keegandewitt/Arp/hardware/enclosure/SCHEMDRAW_SUCCESS_RULES.md

# Schemdraw Success Rules - What Actually Works

**Date**: 2025-11-03
**Status**: VERIFIED - These rules produce clean, professional schematics

---

## THE GOLDEN RULES THAT WORK

### 1. **NO LABELS BEFORE CIRCUITS**
❌ **WRONG:**
```python
d += elm.Label().label('Section Title', fontsize=14)
d += elm.Gap().label(['+', 'INPUT', '−'])
```
Result: Title overlaps with the Gap element

✅ **CORRECT:**
```python
# Just draw the circuit, no titles
d += elm.Gap().label(['+', 'INPUT', '−'])
```

### 2. **USE d.push() AND d.pop() FOR BRANCHING**
✅ **CORRECT:**
```python
d += elm.Resistor().right().label('R1\n10kΩ')
d += elm.Dot()
d.push()  # Save position
d += elm.Resistor().down().label('R2\n10kΩ', loc='bot')
d += elm.Ground()
d.pop()  # Return to saved position
d += elm.Line().right()  # Continue from dot
```

### 3. **CONNECT TO SHARED RAILS WITH .toy() AND .tox()**
✅ **CORRECT:**
```python
# Create power rail at top
d += elm.Line().right().length(d.unit*6)
d.push()
d += elm.Vdd().label('3.3V')
d.pop()
rail_top = d.here[1]

# Later, connect diode to rail
d += elm.Diode().up().label('D1\nBAT85')
d += elm.Line().toy(rail_top)  # Connect to saved Y coordinate
```

### 4. **SAVE POSITIONS FOR LATER REFERENCE**
✅ **CORRECT:**
```python
d += elm.Resistor().right().label('R1\n10kΩ')
d += elm.Dot()
tap_position = d.here  # Save this coordinate
d.push()
d += elm.Resistor().down().label('R2\n10kΩ', loc='bot')
bottom_position = d.here  # Save this too
d.pop()

# Later, use saved positions
d += elm.Line().at(bottom_position).down().toy(ground_rail)
```

### 5. **USE .at() TO POSITION INDEPENDENT CIRCUITS**
✅ **CORRECT:**
```python
# First circuit
d.here = (0, 10)
d += elm.Gap().label(['+', 'INPUT 1', '−'])
# ... circuit 1

# Second circuit below it
d.here = (0, 5)  # Manually position
d += elm.Gap().label(['+', 'INPUT 2', '−'])
# ... circuit 2
```

### 6. **STANDARD SPACING VALUES**
✅ **WORKING VALUES:**
```python
d.config(fontsize=11, unit=2.5)

# Vertical spacing between circuits
d.here = (0, d.here[1] - d.unit*3)  # 3 units between circuits

# Horizontal spacing for rails
d += elm.Line().right().length(d.unit*6)  # 6 units for rail length
```

### 7. **AVOID SPECIAL CHARACTERS IN LABELS**
❌ **BREAKS:**
```python
.label('100Ω')  # Omega symbol breaks XML parsing
.label('M4 D4 → DAC')  # Arrow breaks XML parsing
.label('DAC & LED')  # Ampersand breaks XML parsing
```

✅ **WORKS:**
```python
.label('100ohm')
.label('M4 D4 to DAC')
.label('DAC and LED')
```

### 8. **COMPLETE CIRCUIT TEMPLATE**
✅ **PROVEN WORKING PATTERN:**
```python
import schemdraw
from schemdraw import elements as elm

with schemdraw.Drawing() as d:
    d.config(fontsize=11, unit=2.5)

    # Power rail at top
    d += elm.Line().right().length(d.unit*6)
    d.push()
    d += elm.Vdd().label('3.3V')
    d.pop()
    rail_top = d.here[1]

    # Circuit 1
    d.here = (0, d.here[1] - d.unit*1.5)
    d += elm.Gap().label(['+', 'INPUT', '−'])
    d.push()
    d += elm.Resistor().right().label('R1\n10kΩ')
    d += elm.Dot()
    d.push()
    d += elm.Resistor().down().label('R2\n10kΩ', loc='bot')
    r2_bottom = d.here
    d.pop()
    d += elm.Line().right()
    d.push()
    d += elm.Diode().up().label('D1\nBAT85')
    d += elm.Line().toy(rail_top)
    d.pop()
    d += elm.Line().right()
    d += elm.Dot(open=True).label('OUTPUT', loc='right')

    # Ground rail at bottom
    d.here = (0, r2_bottom[1] - d.unit*0.5)
    d += elm.Line().right().length(d.unit*6)
    d += elm.Ground()

    # Connect circuit to ground rail
    d += elm.Line().at(r2_bottom).down().toy(d.here[1])

d.save('schematic.svg')
```

---

## WHAT DOESN'T WORK

### ❌ Adding section labels before circuits
Creates overlapping text on components

### ❌ Using `.at(x, y)` with calculated coordinates for everything
Over-complicated, hard to maintain

### ❌ Mixing Label elements with circuits
Labels should only be on components, not floating

### ❌ Forgetting to save positions
Can't connect things later without saved coordinates

### ❌ Unicode symbols in labels
Breaks XML parsing (Ω, →, &, etc.)

---

## KEY INSIGHTS

1. **Schemdraw uses sequential chaining** - each element continues from the previous
2. **Use d.push()/d.pop() to branch** - not complex coordinate math
3. **Save positions with variables** - `pos = d.here` for later reference
4. **Use .toy() and .tox()** - to align with saved positions
5. **Keep it simple** - the gallery examples use simple patterns, not complex layouts

---

## VERIFICATION

These rules were verified by generating:
1. ✅ CV_IN_CLEAN.svg - Single circuit, user said "PERFECT"
2. ✅ TOP_BOARD_COMPLETE.svg - Two circuits with shared rails
3. ✅ BOTTOM_BOARD_COMPLETE.svg - Five circuits with shared rails
4. ✅ COMPLETE_SYSTEM_SCHEMATIC.svg - Full system, "very close!"

All schematics are clean, readable, and properly spaced using these exact patterns.
