keegandewitt/Arp/docs/hardware/AUDIT_SUMMARY_INDEX.md

# PRISME Hardware Audit - Summary Index

**Comprehensive Audit Completed:** 2025-11-03
**Main Document:** `COMPREHENSIVE_HARDWARE_AUDIT.md` (1389 lines)

---

## Quick Navigation

### Part 1: Overview & Structure (Sections 1-2)
- **Board Stack Overview:** Two-board vertical stack (INPUT + OUTPUT) with Feather stack on top
- **Pin Allocation:** Complete 21-pin usage matrix for Feather M4
- **File:** Sections 1-2 of COMPREHENSIVE_HARDWARE_AUDIT.md

### Part 2: OUTPUT Board (Bottom) - Sections 3
- **Position:** Bottom of stack, rear connectors for outputs
- **Jacks:** CV OUT, TRIG OUT (dual V/S-Trig), CC OUT, MIDI OUT, MIDI IN, USB-C
- **Key Components:** MCP4728 DAC, S-Trig NPN transistor, 5 white LEDs + 1 RGB LED
- **BOM:** 28 components listed with values and purposes

### Part 3: INPUT Board (Top) - Sections 4
- **Position:** Middle of stack, rear connectors for inputs
- **Jacks:** CV IN, TRIG IN
- **Key Components:** Input protection circuits (voltage dividers + Schottky clamps)
- **BOM:** 12 components listed with values and purposes

### Part 4: Circuit Design Details - Section 5
- **Input Protection:** Voltage divider (0.524×) + 100nF filter + BAT85 clamp
- **CV Output:** 100Ω series + 100nF low-pass filter
- **S-Trig Circuit:** GPIO D10 → 1kΩ → 2N3904 NPN → output jack
- **LED Calculations:** 150Ω current limiting for all LEDs
- **DAC Config:** 1V/octave, 5V reference, 12-bit resolution

### Part 5: Connectors & I2C - Sections 6-7
- **Rear Panel Layout:** All jacks positioned with measurements from left edge
- **I2C Bus:** Shared SDA/SCL, OLED @ 0x3C, MCP4728 @ 0x60
- **Initialization:** Critical sequence (displayio.release → board.I2C → devices)

### Part 6: LED System - Section 8
- **5× White LEDs:** CV IN, CV OUT, CC OUT, MIDI IN, MIDI OUT activity
- **2× RGB LEDs:** TRIG IN (V-Trig=green, S-Trig=red) + TRIG OUT (same modes)
- **Physical Positions:** 7mm right of each jack center, 3.2mm holes

### Part 7: Power & Testing - Sections 9-15
- **Power Budget:** ~100-150mA typical, <200mA maximum
- **Battery Runtime:** 5 hours typical (500mAh LiPo)
- **Decoupling:** 47µF bulk + 0.1µF bypass on each board
- **Verification Checklist:** Pre-assembly, during, and post-assembly tests
- **Troubleshooting:** Common issues and diagnostic procedures

---

## Key Specifications At A Glance

### Hardware
| Item | Value |
|---|---|
| **Board Size** | 90mm × 55mm (×2 boards) |
| **Enclosure** | 70mm × 100mm × 35mm |
| **Main MCU** | Feather M4 CAN Express |
| **DAC** | MCP4728 (4-channel 12-bit I2C) |
| **Total GPIO Used** | 21 out of 26 pins |

### Connector Positions (from left edge)
| Connector | Position | Board |
|---|---|---|
| CV IN | 20mm | INPUT |
| TRIG IN | 32mm | INPUT |
| USB-C | 8mm | OUTPUT |
| CV OUT | 20mm | OUTPUT |
| TRIG OUT | 32mm | OUTPUT |
| CC OUT | 44mm | OUTPUT |
| MIDI OUT | 65mm | OUTPUT |
| MIDI IN | 85mm | OUTPUT |

### LED Positions (from left edge)
| LED | Position |
|-----|---|
| CV IN | 27mm |
| TRIG IN RGB | 39mm |
| CV OUT | 27mm |
| TRIG OUT RGB | 39mm |
| CC OUT | 51mm |
| MIDI OUT | 72mm |
| MIDI IN | 92mm |

### Component Counts
- **Resistors:** 20 total (100Ω, 150Ω, 1kΩ, 10kΩ, 22kΩ)
- **Capacitors:** 13 total (47µF, 0.1µF, 100nF)
- **Diodes:** 2× BAT85 Schottky
- **Transistors:** 1× 2N3904 NPN
- **ICs:** 1× MCP4728
- **Jacks:** 5× 1/8" TRS + 2× 5-pin DIN + 1× USB-C
- **LEDs:** 5× white 3mm + 2× RGB 3mm

---

## Critical Design Decisions

### 1. Input Protection (0.524× Scaling)
**Why:** Protects 3.3V ADC from 0-5V (or higher) external inputs
- Voltage divider: 20kΩ + 22kΩ = 0.524× attenuation
- 5V input → 2.62V at ADC (safe margin)
- Schottky diode provides additional 3.3V clamp
- 100nF filter removes RF noise

### 2. Dual Gate Output Mode (V-Trig AND S-Trig)
**Why:** Compatibility with both modern (Eurorack) and vintage (ARP/Korg) synths
- **V-Trig:** MCP4728 Channel C (0V/5V voltage output)
- **S-Trig:** GPIO D10 + 2N3904 (open circuit / short to GND)
- Same physical jack, software-selectable mode
- RGB LED shows which mode is active

### 3. 1V/Octave Scaling (NOT 2V/octave)
**Why:** Industry standard for pitch control
- MIDI note / 12 = voltage in volts
- 5 octaves range (0-5V) covers full arpeggiator use cases
- No VCO calibration needed if using standard

### 4. MCP4728 over Built-in DAC
**Why:** 12-bit resolution + 0-5V output vs. M4's 10-bit + 0-3.3V
- 68 steps per semitone (high resolution)
- Sufficient for professional-grade CV generation
- I2C addressing allows future expansion (0x60-0x67)

### 5. LED Indicator System (7 LEDs Total)
**Why:** Real-time visual feedback for debugging and performance
- Activity monitoring on all inputs/outputs
- Mode indicators (V-Trig vs. S-Trig)
- MIDI activity pulses
- Low power impact (~20mA when active)

---

## Files Provided

### Main Documentation
1. **COMPREHENSIVE_HARDWARE_AUDIT.md** (1389 lines)
   - Complete specification for all hardware
   - All component values, connections, positions
   - Production-ready schematic reference

2. **AUDIT_SUMMARY_INDEX.md** (this file)
   - Quick navigation and summary
   - Key specs at a glance
   - File references

### Source Documents (Already Exist)
- PIN_ALLOCATION_MATRIX.md - Pin assignments
- PROTOBOARD_LAYOUT.md - Component placement maps
- JACK_WIRING_GUIDE.md - Jack wiring instructions
- BOM.md - Bill of materials
- TRUE_STRIG_CIRCUIT.md - S-Trig circuit details
- CV_OUTPUT_CORRECT_IMPLEMENTATION.md - 1V/octave specs
- MCP4728_CV_GUIDE.md - DAC configuration
- ENCLOSURE_DESIGN.md - Physical layout

---

## How to Use This Audit

### For Creating Schematics
1. Read **Section 3** (OUTPUT Board) for all output circuits
2. Read **Section 4** (INPUT Board) for all input circuits
3. Reference **Section 5** (Circuit Design Details) for calculations
4. Use **Section 6** (Connector Specs) for jack wiring
5. Import pin numbers from **Section 2** (Pin Allocation Matrix)

### For PCB Layout
1. Use **ENCLOSURE_DESIGN.md** for physical dimensions
2. Reference connector positions from **Section 6**
3. Use component BOM counts from **Sections 3-4**
4. Follow power distribution from **Section 9**

### For Assembly Verification
1. Use **Section 13** (BOM) for component procurement
2. Follow **Section 14** (Verification Checklist) during build
3. Reference **Section 15** (Troubleshooting) if issues arise

### For Circuit Testing
1. Use **Section 5** for circuit calculations and expected values
2. Follow testing sequence in **Section 14**
3. Refer to **Section 15** for diagnostic procedures

---

## Key Contact Points for Schematic Creation

### INPUT Board (A3, A4 inputs with protection)
```
CV IN Jack TIP → [R1 10kΩ] → [R2 10kΩ] → [R4 22kΩ→GND]
                                 ↓
                            [R3 10kΩ] → [C3 100nF] → [D1 BAT85] → A3
```

### OUTPUT Board (CV outputs with protection)
```
MCP4728 Ch A → [R1 100Ω] → [C6 100nF] → CV OUT Jack TIP
MCP4728 Ch B → [R2 100Ω] → [C7 100nF] → CC OUT Jack TIP
```

### S-Trig Circuit (GPIO D10 → Transistor)
```
D10 → [1kΩ R5] → 2N3904 Base
                  Collector → [100Ω R6] → TRIG OUT Jack TIP
                  Emitter → GND
```

### I2C Bus
```
D21 (SDA) ──→ OLED (0x3C) + MCP4728 (0x60)
D22 (SCL) ──→ OLED (0x3C) + MCP4728 (0x60)
```

---

## Verification Checklist (Quick Reference)

**Before Assembly:**
- [ ] All resistor values verified
- [ ] All capacitor voltages adequate
- [ ] LED GPIO pins don't conflict
- [ ] Voltage divider scaling confirmed (0.524×)

**During Assembly:**
- [ ] No cold solder joints
- [ ] Capacitor polarities correct
- [ ] Diode polarities marked
- [ ] Resistor bands read correctly

**After Assembly:**
- [ ] 5V rail = 5.0V ±0.2V
- [ ] No short between 5V and GND
- [ ] Voltage divider tap ≈ 2.62V when jack at 5V
- [ ] I2C scan detects 0x60 (MCP4728)
- [ ] All GPIO pins output 3.3V when HIGH
- [ ] All LEDs illuminate when GPIO driven HIGH

---

## Related Documentation

All documents referenced in this audit:
- `/docs/hardware/COMPREHENSIVE_HARDWARE_AUDIT.md` - Main document
- `/docs/hardware/PIN_ALLOCATION_MATRIX.md` - Pin assignments
- `/docs/hardware/PROTOBOARD_LAYOUT.md` - Layout maps
- `/docs/hardware/JACK_WIRING_GUIDE.md` - Wiring instructions
- `/docs/hardware/BOM.md` - Bill of materials
- `/docs/hardware/ENCLOSURE_DESIGN.md` - Physical layout
- `/docs/hardware/I2C_ARCHITECTURE.md` - I2C configuration
- `/docs/hardware/MCP4728_CV_GUIDE.md` - DAC specs

---

**Ready for:** Production-quality schematic creation, PCB layout, assembly, and testing

**Last Updated:** 2025-11-03
**Audit Status:** COMPLETE - All information documented and verified
