keegandewitt/Arp/hardware/enclosure/FINAL_CAD_STATUS.md

# Final CAD Model Status - Complete Component Inventory

**Date:** 2025-11-03
**Status:** ✅ ALL CRITICAL COMPONENTS MODELED

---

## ✅ **COMPLETE - All Critical Components Have CAD Models**

### **Core Electronics (Adafruit Hardware)**

| Component | File | Format | Status |
|---|---|---|---|
| Feather M4 Express | Feather_M4.stl | STL | ✅ Imported |
| OLED FeatherWing 128x64 | OLED_Wing.stl | STL | ✅ Imported |
| MIDI FeatherWing + DIN-5 jacks | MIDI_Wing.stl | STL | ✅ Imported |
| MCP4728 Quad DAC | Adafruit_MCP4728_I2C_Quad_DAC.STEP | STEP | ✅ Have file (placeholder in viz) |

### **Power System**

| Component | Specification | Model Type | Status |
|---|---|---|---|
| **1200mAh LiPo Battery** | Adafruit #258 | OpenSCAD (50×35×8mm soft pouch) | ✅ Modeled |
| **Teyleten Boost Module** | 3.7V→5V @1.5A | OpenSCAD (17×10×4mm with inductor) | ✅ Modeled |

### **Connectors**

| Component | Quantity | File/Model | Status |
|---|---|---|---|
| 3.5mm TRS Jacks (PJ-307) | 6 | pj-307.step | ✅ Have file |
| DIN-5 MIDI Jacks | 2 | Included in MIDI_Wing.stl | ✅ In MIDI Wing |
| USB-C Access | 1 | Direct cutout (9.5×3.8mm) | ✅ Cutout defined |

### **Indicators**

| Component | Quantity | Specification | Status |
|---|---|---|---|
| 3mm White LEDs | 5 | 3V-3.2V @ 20mA, 27/28.5mm leads | ✅ Accurate OpenSCAD model |
| 3mm RGB LEDs | 2 | Common cathode, 4 leads | ✅ Accurate OpenSCAD model |

### **Passive Components**

| Component | Files | Status |
|---|---|---|
| Resistors (100Ω, 150Ω, 1kΩ, 10kΩ, 22kΩ) | .SLDPRT files | ✅ Have files + OpenSCAD models |
| Capacitors (47µF, 0.1µF) | .SLDPRT files | ✅ Have files + OpenSCAD models |
| Schottky Diodes (1N5817) | .SLDPRT file | ✅ Have file + OpenSCAD model |

---

## 📊 **Component Placement in Visualization**

### **BOTTOM Board (OUTPUT) - 108mm × 55mm**

**Back Edge (Left to Right):**
- 10mm: USB-C cutout (9.5×3.8mm rectangular)
- 22mm: CV OUT jack + white LED (29mm)
- 36mm: TRIG OUT jack + RGB LED (43mm)
- 50mm: CC OUT jack + white LED (57mm)
- 72mm: MIDI OUT jack + white LED (84mm, 12mm offset)
- 96mm: MIDI IN jack + white LED (108mm, 12mm offset)

**Components:**
- Right side (93mm from left): MIDI FeatherWing with DIN-5 jacks
- Center (~44mm): MCP4728 Quad DAC
- Front left (15mm): Teyleten boost module
- **Under board (-10mm):** 1200mAh LiPo battery (50×35×8mm)

### **TOP Board (INPUT) - 108mm × 55mm**

**Back Edge (Left to Right):**
- 22mm: CV IN jack + white LED (29mm)
- 36mm: TRIG IN jack + RGB LED (43mm)

**Components:**
- FAR LEFT (5mm): OLED FeatherWing 128x64
- CENTER-RIGHT (55mm): Feather M4 Express

### **Stack Heights**

```
Bottom board:     0.0mm → 1.6mm    (PCB)
Air gap:          1.6mm → 9.6mm   (8mm standoffs)
Top board:        9.6mm → 11.2mm  (PCB)
Air gap:          11.2mm → 21.2mm (10mm standoffs)
Feather/OLED:     21.2mm → 28.2mm (7mm boards, parallel)

Battery UNDER:    -10mm → -2mm    (8mm pouch)
Total volume:     -10mm → 28.2mm  (38.2mm total height)
```

---

## 📁 **Files in Enclosure Folder**

### **CAD Models (Ready for Import)**

**STL Files (OpenSCAD Compatible):**
- Feather_M4.stl (1.6MB)
- OLED_Wing.stl (541KB)
- MIDI_Wing.stl (716KB) - includes DIN-5 jacks!

**STEP Files (Need Conversion or Placeholder):**
- Feather_M4_Express.step
- OLED_FeatherWing.step
- MIDI_FeatherWing.step
- Adafruit_MCP4728_I2C_Quad_DAC.STEP
- pj-307.step (3.5mm TRS jack)
- Battery_1200mAh_258.step

**SolidWorks Files (.SLDPRT - Passive Components):**
- Resistor 100 Ohm.SLDPRT
- Resistor 150 Ohm.SLDPRT
- Resistor 1K Ohm.SLDPRT
- Resistor 10K Ohm.SLDPRT
- Resistor 22K Ohm.SLDPRT
- Capacitor 47uF-25V.SLDPRT
- Capacitor Ceramic 104 0.1uF.SLDPRT
- Schottky Diode 1N5817.SLDPRT

### **OpenSCAD Visualization Files**

- **hardware_stack_with_cad.scad** - Main visualization with all components
- **hardware_stack_accurate.scad** - Previous version with geometric shapes
- **hardware_complete_preview.png** - Latest render (generating...)

### **Documentation**

- **COMPLETE_COMPONENT_INVENTORY.md** - Detailed component list and status
- **MISSING_CAD_MODELS.md** - Component sourcing and CAD model links
- **CAD_IMPORT_STATUS.md** - Integration status and conversion notes
- **FINAL_CAD_STATUS.md** - This document

---

## 🎯 **What's Modeled**

### **Accurately Modeled in OpenSCAD:**

1. ✅ **Protoboards** (108×55×1.6mm with jack cutouts)
2. ✅ **Feather M4, OLED Wing, MIDI Wing** (imported STL files)
3. ✅ **1200mAh LiPo Battery** (soft-cornered pouch with JST connector)
4. ✅ **Teyleten Boost Module** (17×10mm PCB with inductor and SMD components)
5. ✅ **3mm LEDs** (white and RGB with accurate specs: 3mm lens, 5.4mm height, proper lead lengths)
6. ✅ **MCP4728 DAC** (placeholder box, STEP file available for conversion)
7. ✅ **Passive Components** (resistors, capacitors, diodes - simplified geometry)
8. ✅ **Standoffs** (M3 and M2.5 between boards)

### **Defined for Enclosure:**

9. ✅ **3.5mm TRS jack holes** (6mm diameter, STEP file available)
10. ✅ **DIN-5 MIDI jack holes** (15.5mm diameter, included in MIDI Wing)
11. ✅ **USB-C cutout** (9.5×3.8mm rectangular direct access)

---

## 🔧 **Optional Enhancements** (Not Critical)

### **Can Add If Desired:**

- **Protoboard perforation pattern** (0.1" grid holes)
- **Wire routing** (power distribution, I2C connections)
- **Slide switch** (power control - not yet specified/modeled)
- **Detailed standoff threading** (currently simple cylinders)
- **Heat shrink tubing** (on solder joints)

### **File Conversions (For Perfect Accuracy):**

- Convert STEP files to STL using FreeCAD
  - pj-307.step → pj-307.stl (for actual jack geometry)
  - Battery_1200mAh_258.step → Battery_1200mAh_258.stl
  - Adafruit_MCP4728_I2C_Quad_DAC.STEP → MCP4728.stl
- Convert SLDPRT files to STL (optional - current simplified models work)

---

## 📐 **Key Dimensions for Enclosure Design**

### **Internal Clearances Needed:**

**Width:** 108mm (protoboard length) + 5mm clearance = **113mm minimum**

**Depth:** 55mm (protoboard width) + back panel jacks depth:
- 3.5mm jacks: ~20mm behind panel
- DIN-5 jacks: ~25mm behind panel
- **Total depth:** ~80-85mm

**Height (stacking from bottom):**
- Battery space: 10mm below bottom board
- Bottom board + components: 10mm
- Air gap + standoffs: 8mm
- Top board + components: 10mm
- Feather/OLED: 7mm + standoffs 10mm = 17mm
- Top clearance: 5mm
- **Total height:** ~60-65mm

**Critical Spacing:**
- MIDI LED offset: **12mm** (not 7mm!) to clear 15.5mm jack holes
- LED press-fit holes: 3.2mm diameter (for 3mm LEDs)
- Jack spacing from BOM layout

---

## ✅ **SUMMARY - Visualization Complete**

**All critical components are now modeled or have CAD files available.**

The `hardware_stack_with_cad.scad` file contains:
- ✅ Real Adafruit board STL imports (Feather, OLED, MIDI with jacks)
- ✅ Accurate battery model (1200mAh soft pouch)
- ✅ Accurate boost module model (based on product image)
- ✅ Accurate LED models (with exact specifications)
- ✅ Proper component placement per PROTOBOARD_LAYOUT.md
- ✅ Correct stack heights and board separation
- ✅ All jack positions and LED offsets

**Ready for enclosure design with accurate internal dimensions and component clearances!**

---

**Generated:** 2025-11-03
**OpenSCAD File:** hardware_stack_with_cad.scad
**Latest Render:** hardware_complete_preview.png (generating)
