keegandewitt/Arp/ENCLOSURE_ROADMAP.md

# Enclosure Roadmap

## Project Overview
Custom enclosure for MIDI Arpeggiator based on Adafruit M4 Express with FeatherWings stack.

## Design Decisions (All Confirmed ✅)
- ✓ **Form Factor:** Horizontal Desktop Box (desktop-only, no portability features)
- ✓ **Manufacturing:** 3D Printing with Fusion 360 on Bambu Labs A1 Mini (no AMS-lite)
- ✓ **Finish:** Raw 3D print (no painting or post-processing)
- ✓ **Power & Charging:** USB-C on M4 Feather CAN (charging + programming)
- ✓ **5V Boost:** Teyleten Multi-Function Boost Module (3.7V→5V @ 1.5A, ~$0.70 each)
- ✓ **Power Switch:** Slide switch Model 805 - acts as power distribution/splitter point
- ✓ **CV Output:** Adafruit MCP4728 Quad DAC (4 channels, 0-5V, 12-bit, I2C)
- ✓ **CV Labeling:** Generic "CV 1-4" (reprogrammable for any function)
- ✓ **External Controls:** None - using only OLED Wing's 3 buttons
- ✓ **No Second MIDI FeatherWing:** Using external DAC instead

## Hardware Components to Accommodate

### Electronics Stack
- **Adafruit Feather M4 CAN Express** (base board, main controller with built-in USB-C LiPo charging)
- **OLED FeatherWing** (128x32 display with buttons A, B, C)
- **MIDI FeatherWing** (DIN-5 MIDI jacks for note data IN/OUT)
- **Teyleten Multi-Function Boost Module** (3.7V→5V @ 1.5A, adjustable voltage)
- **MCP4728 Quad DAC Breakout** (I2C, 4-channel 12-bit DAC, 0-5V output)
- **LiPo Battery** (500-1200mAh, ~50x34x6mm typical)
- **Slide Switch Model 805** (power distribution point)

### Connectors & External Access
- **USB-C Port** (M4 Express) - **Direct access for charging + programming**
- **Slide Switch Model 805** (power distribution) - **Side panel, controls all power**
- **MIDI Connections (Standard MIDI FeatherWing):**
  - 1x MIDI IN Jack (5-pin DIN) - Note data input from keyboard
  - 1x MIDI OUT Jack (5-pin DIN) - Arpeggiated output to synthesizer
- **CV Outputs (MCP4728 Quad DAC):**
  - 4x 1/8" TRS jacks (0-5V, 1V/octave compatible)
  - Panel-mount 3.5mm mono jacks required
  - Perfect for vintage synths (Moog, ARP, Roland, etc.)

### Physical Dimensions Reference

**FeatherWing Stack:**
- **M4 Feather CAN Express:** 50.8mm x 22.86mm x ~8mm (2" x 0.9" x 0.3" with headers)
- **MIDI FeatherWing:** 50.8mm x 22.86mm x ~8mm
- **OLED FeatherWing:** 50.8mm x 22.86mm x ~15mm (with display and buttons)
- **Stack Height (total):** ~30-40mm (depending on header/spacer configuration)
- **OLED Display Area:** 128x32 pixels (~25mm x 10mm viewing area)

**Additional Modules:**
- **Teyleten Boost Module:** 22mm x 11mm x 3.6mm (0.87" x 0.43" x 0.14")
- **Adafruit MCP4728 DAC:** 25.7mm x 17.8mm x 4.6mm (1.0" x 0.7" x 0.2")
- **Combined footprint:** Can mount side-by-side in ~50mm x 20mm area

**Panel Components:**
- **DIN-5 MIDI Jack:** 14mm diameter mounting hole (x2 for MIDI IN/OUT)
- **1/8" TRS Jack (3.5mm):** 6mm diameter mounting hole (x4 for CV outputs 1-4)
- **USB-C Port (M4):** 9mm x 4mm cutout (with clearance)
- **Slide Switch Model 805:** See `_hardware_files/805 slide switch.f3d` for exact dimensions

**Battery:**
- **LiPo (500-1200mAh):** Approximately 50mm x 34mm x 6mm (varies by capacity)

**Enclosure Planning:**
- **Minimum internal space:** ~120mm x 80mm x 50mm (estimate)
- **Module placement:** Teyleten Boost + MCP4728 mount beside stack on foam tape or standoffs

---

## Phase 1: Design Requirements & Planning

### 1.1 Form Factor Decision ✓ CONFIRMED
**Selected:** Horizontal Desktop Box
- Top panel: OLED display window with button access
- Front panel: MIDI jacks (panel-mount DIN-5 connectors)
- Rear panel: USB-C port cutout (direct access to M4 Express port)
- Side panel: Slide switch cutout for battery disconnect
- Pros: Stable, traditional MIDI device look, easy to access all controls
- Note: Position M4 Express with USB-C facing rear panel for easy cable access
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
