keegandewitt/Arp/hardware/enclosure/archive_openscad_attempts/COMPLETE_COMPONENT_INVENTORY.md

# Complete Component Inventory for Perfect 3D Rendering

**Date:** 2025-11-03
**Purpose:** Detailed status of every component needed for accurate enclosure visualization

---

## ✅ COMPONENTS WE HAVE (CAD Models)

### Core Electronics - Adafruit Hardware

| Component | Quantity | File(s) | Format | Status |
|---|---|---|---|---|
| **Feather M4 Express** | 1 | Feather_M4.stl, Feather_M4_Express.step | STL, STEP | ✅ Complete |
| **OLED FeatherWing 128x64** | 1 | OLED_Wing.stl, OLED_FeatherWing.step | STL, STEP | ✅ Complete |
| **MIDI FeatherWing (with DIN-5 jacks!)** | 1 | MIDI_Wing.stl, MIDI_FeatherWing.step | STL, STEP | ✅ Complete with jacks |
| **MCP4728 Quad DAC** | 1 | Adafruit_MCP4728_I2C_Quad_DAC.STEP | STEP | ✅ Complete |

### Connectors

| Component | Quantity | File(s) | Dimensions | Status |
|---|---|---|---|---|
| **3.5mm TRS Jacks (PJ-307)** | 6 | pj-307.step | 15×11×9mm | ✅ Complete |
| **DIN-5 MIDI Jacks** | 2 | Included in MIDI_Wing.stl | 15.5mm hole | ✅ Included in MIDI Wing |

### Passive Components (SolidWorks .SLDPRT format)

| Component | Quantity | File(s) | Status |
|---|---|---|---|
| **Resistor 100Ω** | 2 | Resistor 100 Ohm.SLDPRT | ✅ Have |
| **Resistor 150Ω** | 5 | Resistor 150 Ohm.SLDPRT | ✅ Have |
| **Resistor 1kΩ** | Variable | Resistor 1K Ohm.SLDPRT | ✅ Have |
| **Resistor 10kΩ** | Variable | Resistor 10K Ohm.SLDPRT | ✅ Have |
| **Resistor 22kΩ** | Variable | Resistor 22K Ohm.SLDPRT | ✅ Have |
| **Capacitor 47µF** | 2 | Capacitor 47uF-25V.SLDPRT | ✅ Have |
| **Capacitor 0.1µF ceramic** | 8+ | Capacitor Ceramic 104 0.1uF.SLDPRT | ✅ Have |
| **Schottky Diode 1N5817** | 2 | Schottky Diode 1N5817.SLDPRT | ✅ Have |

### LEDs (Modeled in OpenSCAD)

| Component | Quantity | Specifications | Status |
|---|---|---|---|
| **3mm White LEDs** | 5 | Lens: 3mm, Height: 5.4mm, Leads: 27/28.5mm, 3V-3.2V @ 20mA | ✅ Accurate model in .scad |
| **3mm RGB LEDs** | 2 | Lens: 3mm, Height: 5.4mm, 4 leads, Common cathode | ✅ Accurate model in .scad |

---

## ⚠️ COMPONENTS WE'RE MISSING (Priority Order)

### 🔴 HIGH PRIORITY - Affects Enclosure Dimensions & Clearances

#### 1. LiPo Battery
- **Purpose:** Power source, affects internal volume
- **Specifications:**
  - **Capacity:** 500mAh OR 1200mAh (which do you have?)
  - **Voltage:** 3.7V single-cell
  - **Connector:** JST 2-pin
  - **Dimensions (500mAh):** ~30mm × 34mm × 6mm
  - **Dimensions (1200mAh):** ~35mm × 50mm × 8mm
  - **Type:** Flexible pouch battery
- **✅ CAD MODELS AVAILABLE:**
  - **Adafruit #258 (1200mAh):** https://github.com/adafruit/Adafruit_CAD_Parts/blob/main/258%201200mAh%20lipo/258%201200mAh%20lipo.step
  - **Adafruit #328 (2500mAh):** https://github.com/adafruit/Adafruit_CAD_Parts/blob/main/328%202500mAh%20battery/328%202500mAh%20battery.step
- **What I need:**
  - Which battery capacity are you using? (I can download the correct STEP file)

#### 2. USB-C Panel Mount Breakout
- **Purpose:** Access to Feather M4 USB-C from back panel
- **Specifications:**
  - **Panel cutout:** 9.5mm × 3.8mm rectangular
  - **Depth behind panel:** ~15mm
  - **Type:** Female USB-C jack on small PCB breakout
- **What I need:**
  - CAD model (STL/STEP) if available, OR
  - Product link/part number, OR
  - Can model as simple rectangular cutout if using direct access to Feather's onboard USB-C

#### 3. Teyleten Boost Module (3.7V → 5V @ 1.5A)
- **Purpose:** Boosts LiPo voltage to 5V for system
- **Specifications:**
  - **Estimated dimensions:** ~17mm × 10mm × 4mm
  - **Type:** Generic DC-DC boost converter
- **What I need:**
  - CAD model if available, OR
  - Product photo showing top/side views with ruler, OR
  - Exact PCB dimensions (L×W×H)
  - Can model as simple rectangular box with key components indicated

#### 4. Slide Switch (Model 805)
- **Purpose:** Power distribution (battery → M4 + boost)
- **Specifications:**
  - **Type:** SPDT slide switch
  - **Mounting:** Panel mount or PCB mount?
  - **Estimated dimensions:** ~8mm × 3mm × 5mm
- **What I need:**
  - CAD model if available, OR
  - Product link/datasheet, OR
  - Photo with dimensions
  - Can model as simple rectangular box

---

### 🟡 MEDIUM PRIORITY - Visual Accuracy & Component Placement

#### 5. 2N3904 NPN Transistor
- **Purpose:** S-Trig mode switching circuit
- **Quantity:** 1
- **Package:** TO-92 through-hole
- **Dimensions:** ~4.5mm × 5mm × 4mm
- **What I need:**
  - CAD model (probably in passive components library), OR
  - Can search GrabCAD, OR
  - Can model as simple TO-92 package shape

#### 6. Protoboard Exact Model
- **Current:** Modeling as simple rectangle 108mm × 55mm × 1.6mm
- **Reality:** ElectroCookie protoboard with hole pattern
- **What I need:**
  - Do you want the actual protoboard hole pattern modeled?
  - If yes, need grid spacing (typically 2.54mm / 0.1")
  - Can add realistic perfboard holes for visualization

---

### 🟢 LOW PRIORITY - Optional for Complete Realism

#### 7. Standoffs & Hardware
- **M3 Standoffs** (8-10mm female-female hex brass)
  - Quantity: 4-8
  - Dimensions: 5mm hex × specified length
  - **Can model as:** Simple hex cylinders (easy)

- **M2.5 Standoffs** (10-15mm female-female hex brass)
  - Quantity: 8-12
  - Dimensions: 4.5mm hex × specified length
  - **Can model as:** Simple hex cylinders (easy)

- **M3 Screws & Nuts**
  - Quantity: 10-15 each
  - **Can model as:** Generic screw/nut geometry (easy)

- **M2.5 Screws & Nuts**
  - Quantity: 10-20 each
  - **Can model as:** Generic screw/nut geometry (easy)

#### 8. Wire & Cabling
- **22-24 AWG stranded wire** for power distribution
- **Jumper wires** (F/F, M/F) for I2C connections
- **What I need:**
  - Do you want wire routing visualized?
  - If yes, I can model realistic wire paths
  - If no, can skip entirely

#### 9. Heat Shrink Tubing
- **Purpose:** Insulating solder joints
- **Can skip for visualization** unless you want extreme detail

---

## 📊 SUMMARY - What I Need From You

### Critical Items (Please Provide):

1. **LiPo Battery:**
   - Which capacity? (500mAh or 1200mAh)
   - Exact dimensions of YOUR battery (L×W×H)
   - Product link or CAD model if available

2. **USB-C Breakout:**
   - Are you using a panel mount extension OR direct cutout?
   - If extension: product link or dimensions
   - If direct cutout: confirm 9.5mm × 3.8mm is correct

3. **Boost Module:**
   - Product link or photo with dimensions
   - PCB dimensions (L×W×H)

4. **Slide Switch:**
   - Product link/part number
   - Mounting type (panel or PCB)
   - Dimensions

### Optional Items (If You Want Extra Detail):

5. **Protoboard holes:** Do you want perfboard pattern modeled?
6. **Wire routing:** Do you want wiring visualized?
7. **Hardware:** Simple geometric standoffs/screws OK, or need exact models?

---

## 🎯 Current Status

**CRITICAL COMPONENTS:** 4/4 complete (100%)
- ✅ Feather boards (all 3)
- ✅ MCP4728 DAC
- ✅ 3.5mm TRS jacks
- ✅ DIN-5 MIDI jacks (in MIDI Wing)

**SUPPORTING COMPONENTS:** 4/8 needed
- ⚠️ Battery (NEED)
- ⚠️ USB-C breakout (NEED)
- ⚠️ Boost module (NEED)
- ⚠️ Slide switch (NEED)
- ✅ LEDs (modeled)
- ✅ Passives (have files)
- ⏸️ Transistor (optional)
- ⏸️ Protoboard pattern (optional)

**OPTIONAL COMPONENTS:** 0/3 (can skip or model generically)
- ⏸️ Standoffs/hardware
- ⏸️ Wire routing
- ⏸️ Heat shrink

---

## 📐 Conversion Notes

**SLDPRT Files (SolidWorks):**
- We have resistors, capacitors, diodes in .SLDPRT format
- OpenSCAD cannot import SLDPRT directly
- **Options:**
  1. Convert to STL using FreeCAD (batch conversion)
  2. Model as simple geometry (cylinders for resistors, etc.)
  3. For detailed visualization, conversion recommended
- **Current approach:** Using simplified geometry modules in OpenSCAD

**STEP Files:**
- We have STEP files for most components
- OpenSCAD cannot import STEP directly
- **Options:**
  1. Convert to STL using FreeCAD
  2. Use placeholder geometry
- **Current status:** MCP4728 and PJ-307 have STEP files, need conversion or placeholders

---

## 🔧 Action Items for Perfect Rendering

### For You:
1. Provide battery dimensions/model
2. Provide USB-C breakout info
3. Provide boost module dimensions/model
4. Provide slide switch info
5. Decide: detailed visualization (with protoboard holes, wiring) or simplified?

### For Me:
1. Convert STEP files to STL (MCP4728, PJ-307) OR create accurate placeholder geometry
2. Integrate all new components into OpenSCAD
3. Add battery, USB-C, boost module, switch models
4. Optional: Add protoboard perforation pattern
5. Optional: Model wire routing
6. Generate final high-quality renders

---

**Questions? Please provide details for items 1-4 above and I'll integrate them immediately!**
