keegandewitt/Arp/hardware/enclosure/Battery_1200mAh_258.step

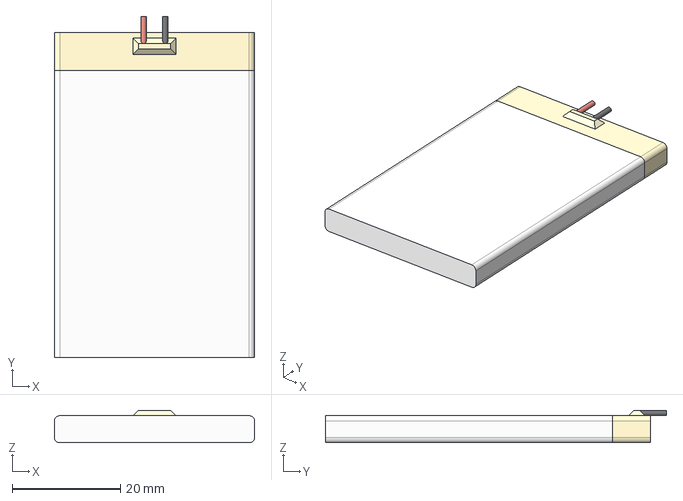
[picture p15: CAD file, 2025-11-03]
hardware/enclosure/Battery_1200mAh_258.step
37.0 x 63.0 x 6.00 mm
