keegandewitt/Arp/hardware/enclosure/prisme_lid_corrected.stl

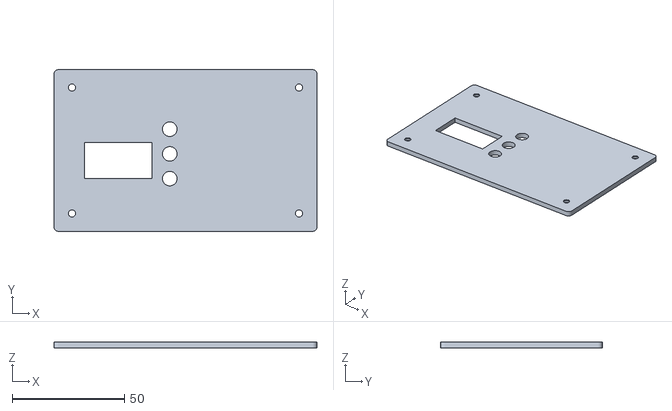
[picture p16: CAD file, 2025-11-03]
hardware/enclosure/prisme_lid_corrected.stl
117.0 x 72.0 x 2.50
