keegandewitt/Arp/hardware/enclosure/prisme_lid.stl

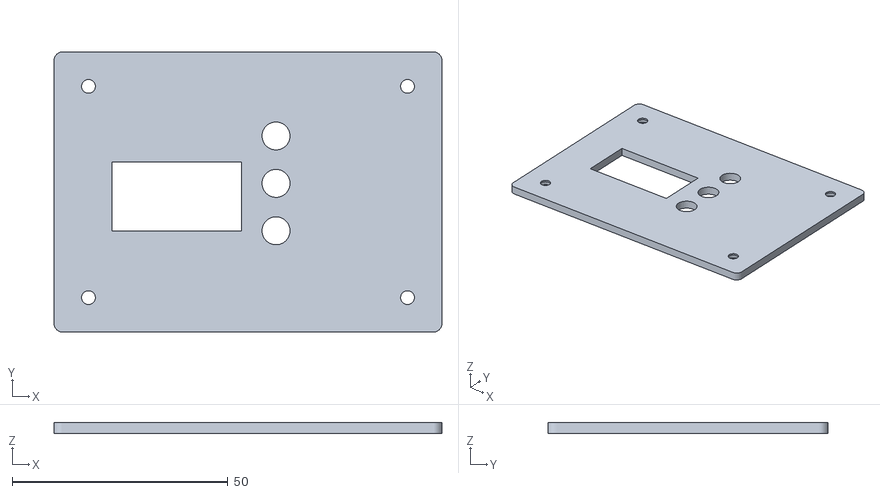
[picture p17: CAD file, 2025-11-03]
hardware/enclosure/prisme_lid.stl
90.0 x 65.0 x 2.50
