keegandewitt/Arp/hardware/enclosure/prisme_box.stl

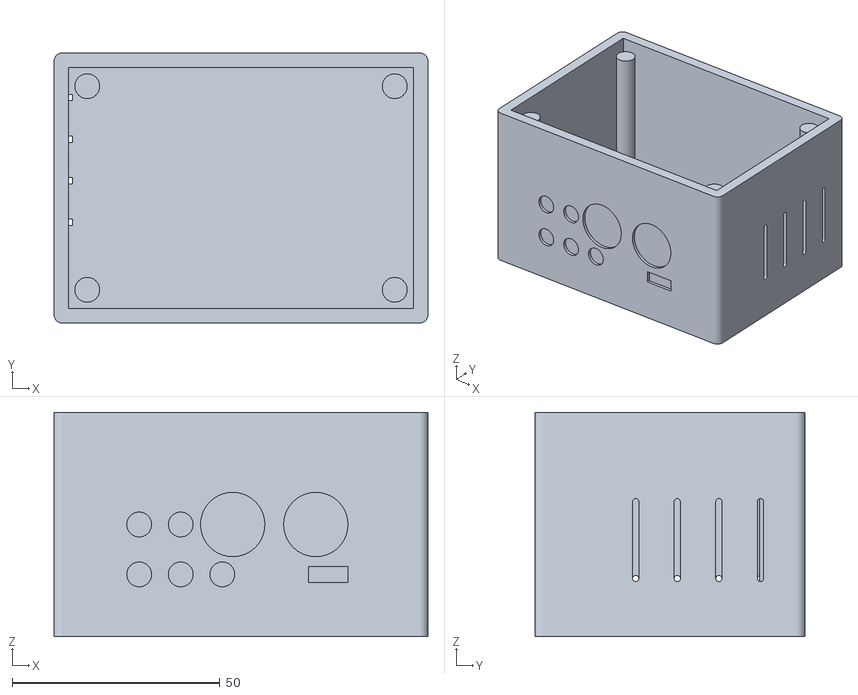
[picture p18: CAD file, 2025-11-03]
hardware/enclosure/prisme_box.stl
90.0 x 65.0 x 54.0
