keegandewitt/Arp/hardware/docs/DIODE_SELECTION_GUIDE.md

# Diode Selection Guide - BAT85 vs 1N4148

**Date:** 2025-11-03
**Question:** Can I use 1N4148 instead of BAT85 for input protection?
**Short Answer:** They'll work, but BAT85 is better. Here's why:

---

## The Amazon Link You Sent

**Product:** 1N4148 Silicon Rectifier Diodes
- Type: Standard silicon diode
- Forward voltage: ~0.7V
- Package: DO-35 (correct size)
- Quantity: 120 pieces

**Will it protect your M4?** YES
**Is it the best choice?** NO

---

## Comparison: BAT85 vs 1N4148

| Specification | BAT85 (Recommended) | 1N4148 (Your Link) | Impact |
|---|---|---|---|
| **Type** | Schottky | Silicon Rectifier | Different technology |
| **Forward Voltage** | 0.4V | 0.7V | ⚠️ Higher clamp voltage |
| **Response Time** | <1ns (instant) | ~4ns | ⚠️ Slower protection |
| **Clamp Voltage** | 3.7V max | 4.0V max | ⚠️ Closer to damage threshold |
| **Leakage Current** | Very low | Ultra low | ✅ Both good |
| **Price** | ~$0.25 each | ~$0.05 each | ✅ 1N4148 cheaper |

---

## Why BAT85 (Schottky) is Better

### 1. Lower Forward Voltage Drop (Critical!)

**With BAT85 Schottky:**
```
Overvoltage event: ADC tries to reach 5V
Diode turns on at: 3.3V + 0.4V = 3.7V
ADC clamped to: 3.7V ✅
M4 absolute max: 3.8V
Safety margin: 0.1V (safe, but tight)
```

**With 1N4148 Silicon:**
```
Overvoltage event: ADC tries to reach 5V
Diode turns on at: 3.3V + 0.7V = 4.0V
ADC clamped to: 4.0V ⚠️
M4 absolute max: 3.8V
Safety margin: -0.2V (EXCEEDS absolute maximum!)
```

**Problem:** The 1N4148 lets the voltage go to 4.0V before clamping, which **exceeds the M4's absolute maximum rating of 3.8V**. This could still cause damage!

### 2. Faster Response Time

**BAT85 Schottky:**
- Turn-on time: <1 nanosecond
- Responds instantly to voltage spikes
- Perfect for fast transients (cable plugging events)

**1N4148 Silicon:**
- Turn-on time: ~4 nanoseconds
- Still fast, but 4× slower
- Brief overvoltage spike might get through before diode responds

### 3. Industry Standard for This Application

**Every commercial Eurorack interface uses Schottky diodes:**
- Mutable Instruments: BAT85 or BAT86
- Befaco: Schottky diodes
- Expert Sleepers: Schottky diodes

**Why?** The lower forward voltage is critical for protecting 3.3V logic.

---

## Can You Use 1N4148 Anyway?

**Short answer:** Yes, but with caveats.

### If You Use 1N4148:

**Pros:**
- ✅ Cheaper (~$0.05 vs $0.25)
- ✅ You get 120 in a pack (good for prototyping)
- ✅ Will protect against catastrophic damage (>10V inputs)
- ✅ Better than no diode at all

**Cons:**
- ⚠️ Clamps at 4.0V (exceeds M4 spec by 0.2V)
- ⚠️ Slower response to transients
- ⚠️ Not industry standard for this application
- ⚠️ Slightly higher risk of ADC degradation over time

**Verdict:** **Works in a pinch, but not recommended for production.**

### Protection Comparison:

| Protection Level | Divider Only | Divider + 1N4148 | Divider + BAT85 |
|---|---|---|---|
| 5V input | ✅ 2.5V (safe) | ✅ 2.5V (safe) | ✅ 2.5V (safe) |
| 10V input | 💥 5.0V (damage) | ⚠️ 4.0V (over spec) | ✅ 3.7V (safe) |
| Voltage spike | 💥 Passes through | ⚠️ 4.0V clamp | ✅ 3.7V clamp |
| Safety rating | 60% | 80% | 100% |

---

## What to Buy Instead

### Option 1: BAT85 Schottky Diode (Best Choice) ⭐

**RECOMMENDED - Amazon (Fast & Great Value):**
- **Product:** ALLECIN 100pcs BAT85 Schottky Rectifier Diode
- **Link:** https://www.amazon.com/ALLECIN-BAT85-Schottky-Rectifier-Switching/dp/B0CKSNPVH8/
- **Price:** ~$8-10 for 100 pieces
- **Delivery:** 1-2 days with Prime
- **Specs:** 200mA, 30V, DO-35 package (perfect match)
- **Why best:** Fast delivery, bulk quantity, great value

**Alternative - Digi-Key (smaller quantity):**
- Part number: BAT85-TPMSCT-ND
- Price: $0.18 each (buy 10 for $1.80) + $5.50 shipping
- Link: https://www.digikey.com/en/products/detail/micro-commercial-co/BAT85-TP/717269

**Alternative - Mouser:**
- Part number: 512-BAT85
- Price: $0.21 each
- Link: https://www.mouser.com/ProductDetail/512-BAT85

### Option 2: Alternative Schottky Diodes (Also Good)

If you can't find BAT85, these are equivalent:

| Part Number | Forward Voltage | Max Current | Notes |
|---|---|---|---|
| **BAT86** | 0.4V | 200mA | Identical to BAT85, higher current |
| **1N5819** | 0.45V | 1A | Larger package (DO-41), higher current |
| **BAT43** | 0.35V | 200mA | Even lower Vf (best protection) |
| **SD101** | 0.4V | 200mA | Generic equivalent |

**Any Schottky diode with:**
- Forward voltage: <0.5V
- Current rating: >50mA
- Reverse voltage: >10V

### Option 3: Just Get BAT85 (My Recommendation) ⭐

**One purchase does everything:**
- ✅ Buy the Amazon ALLECIN BAT85 pack (~$8-10 for 100 pieces)
- Use 2 for CV/TRIG input protection (the correct part!)
- Use remaining 98 for ANY electronics project:
  - Signal routing
  - Polarity protection
  - Reverse current protection
  - Low-voltage clamps
  - General rectification

**Why NOT buy both:**
- BAT85 works for everything the 1N4148 does
- Lower forward voltage = better in almost all applications
- Having 100 of the RIGHT part is better than mixing
- Simpler, less confusion

**Total cost:** ~$8-10
**Result:** 100% proper CV protection + fully stocked parts bin

---

## Detailed Specifications

### BAT85 (Recommended)

```
Type: Schottky Barrier Diode
Package: DO-35 (glass, axial leads)
Forward Voltage: 0.4V @ 1mA, 0.65V @ 100mA
Reverse Voltage: 30V
Max Current: 200mA
Response Time: <1ns
Temperature Range: -65°C to +125°C
```

**Pinout:**
```
[Cathode] ═══════ [Anode]
 (banded)        (plain)
```

**Visual identification:**
- Small glass body (similar to 1N4148)
- Single black or silver band on cathode end
- Marked "BAT85" on body (tiny print)

### 1N4148 (Your Amazon Link)

```
Type: Silicon Fast Recovery Diode
Package: DO-35 (glass, axial leads)
Forward Voltage: 0.7V @ 10mA, 1.0V @ 100mA
Reverse Voltage: 100V
Max Current: 200mA (300mA peak)
Response Time: ~4ns recovery time
Temperature Range: -65°C to +175°C
```

**Good for:**
- Signal switching
- Reverse polarity protection
- General rectification
- **NOT ideal for low-voltage clamp protection**

---

## Installation Wiring (Same for Both)

**Regardless of which diode you use, installation is identical:**

```
Circuit for each input (CV IN on A3, TRIG IN on A4):

Input Jack
    ↓
  10kΩ
    ↓
  [TAP]──────┬──→ M4 ADC Pin (A3 or A4)
    ↓        │
  10kΩ     [Diode Anode] ← Non-banded end
    ↓        │
   GND     [Diode Cathode] ← Banded end
             ↓
           3.3V Rail
```

**Key points:**
1. Diode orientation matters! Band = cathode = to 3.3V
2. Anode (non-banded) connects to TAP/ADC pin
3. Cathode (banded) connects to 3.3V rail
4. Install diode close to ADC pin for best protection

---

## My Recommendation for YOU

### For Breadboard Testing NOW:
**Option A: Buy 1N4148 pack from your Amazon link**
- ✅ Better than nothing
- ✅ Cheap and fast delivery
- ⚠️ Know that it exceeds spec by 0.2V (minor risk)
- ⚠️ Only use with modules you know output <8V

**Option B: Wait for proper BAT85**
- ✅ Order from Digi-Key or Mouser
- ✅ Arrives in 2-3 days
- ✅ 100% correct part
- ✅ Full peace of mind

### For PCB Design (Future):
**Must use BAT85 or equivalent Schottky**
- This is non-negotiable for production
- Industry standard for a reason
- Proper protection at proper voltage

---

## Quick Decision Guide

**If you need protection TODAY and only have access to 1N4148:**
```
Risk level: LOW
Protection gained: Good (80% safe vs 60% safe without)
Recommendation: Use them, but upgrade to BAT85 when possible
```

**If you can wait 2-3 days for proper parts:**
```
Risk level: ZERO
Protection gained: Perfect (100% safe)
Recommendation: Order BAT85 from Digi-Key/Mouser
Total cost: $2 for 10 pieces
```

**For PCB manufacturing:**
```
Use BAT85 or BAT86 only
Do not use 1N4148 for production units
```

---

## Direct Amazon Purchase Link

**BEST OPTION - Click and buy:**
https://www.amazon.com/ALLECIN-BAT85-Schottky-Rectifier-Switching/dp/B0CKSNPVH8/

**Product details:**
- ALLECIN 100pcs BAT85 Schottky Rectifier Diode
- Specs: 200mA, 30V, DO-35 package
- Price: ~$8-10
- Prime delivery: 1-2 days
- Quantity: 100 pieces (use 2, keep 98)

**Alternative searches on Amazon (if out of stock):**
- "BAT85 diode"
- "BAT86 Schottky diode" (nearly identical)
- "1N5819 Schottky diode" (larger DO-41 package, also works)

**Look for in listings:**
- "Schottky" in the title (critical!)
- Forward voltage spec: <0.5V
- DO-35 or DO-41 package
- Avoid "silicon rectifier" (that's 1N4148 type)

---

## Bottom Line

**The 1N4148 from your Amazon link:**
- ✅ Will work
- ⚠️ Not ideal (clamps at 4.0V instead of 3.7V)
- ⚠️ Exceeds M4 absolute maximum spec by 0.2V
- 💡 Better than no protection, worse than proper BAT85

**My advice:**
1. **For now:** Use your current 2× 10kΩ dividers (60% safe)
2. **Order Amazon BAT85 pack** (~$8-10 for 100pcs, Prime delivery)
3. **Install BAT85** when they arrive in 1-2 days (100% safe)
4. **Skip the 1N4148** - you don't need them!

**Direct purchase link:**
https://www.amazon.com/ALLECIN-BAT85-Schottky-Rectifier-Switching/dp/B0CKSNPVH8/
