keegandewitt/Arp/docs/hardware/MCP4728_WORKING_SETUP.md

# MCP4728 Working Setup - 5V Operation (No Level Shifters Required!)

**Date:** 2025-10-24
**Status:** ✅ TESTED AND WORKING

---

## Summary

**Good news:** The MCP4728 DAC works perfectly at 5V power with 3.3V I2C logic from the Feather M4, **without requiring level shifters!**

While technically out of spec, the MCP4728 reliably accepts 3.3V logic on SDA/SCL even when powered at 5V. This simplifies the build significantly.

---

## Working Configuration

### Power Supply
```
LiPo Battery (3.7V nominal, 4.2V fully charged)
    ↓
Feather M4 BAT pin
    ↓
Powerboost Module (configured for 5V output)
    ↓
MCP4728 VDD (5.18V measured)
```

**Result:** MCP4728 outputs full 0-5V range for proper CV control.

### I2C Connection (3.3V Logic)
```
Feather M4 (3.3V I2C)
    ├─ D21 (SDA) ──────────┐
    ├─ D22 (SCL) ──────────┤
    └─ GND ────────────────┤
                           ↓
                    MCP4728 DAC
                    (powered at 5V)
```

**Connection Method:** Jumper wires from M4 stacking headers to MCP4728
- M4 **D21 (SDA)** → MCP4728 **SDA**
- M4 **D22 (SCL)** → MCP4728 **SCL**
- M4 **GND** → MCP4728 **GND** (common ground with Powerboost)

**IMPORTANT:** Do NOT use STEMMA QT cable - it creates a voltage conflict between 3.3V (OLED) and 5V (MCP4728) power rails.

### I2C Bus Topology
```
Feather M4 Stacking Headers
    ├─── OLED FeatherWing (0x3C) - via stacked headers
    └─── MCP4728 DAC (0x60) - via jumper wires from headers
```

Both devices share the same I2C bus from the M4's stacking headers.

---

## Why Level Shifters Aren't Needed (Practically)

### The Spec Says...
- MCP4728 datasheet: I2C logic levels should match VDD voltage
- VDD = 5V → SDA/SCL should be 5V logic
- M4 outputs 3.3V logic

### But In Reality...
- **3.3V is recognized as "HIGH" by 5V logic** (threshold typically ~2.5V)
- **Tested and verified:** All I2C communication works reliably
- **Output tested:** Full 0-5V range confirmed on all 4 DAC channels
- **No errors:** No I2C communication failures observed

### Trade-offs
✅ **Pros:**
- Simpler circuit (no level shifter chips needed)
- Lower cost ($3-5 saved per unit)
- Fewer components to fail
- Works reliably in testing

⚠️ **Cons:**
- Technically out of spec
- May be sensitive to noise or long cable runs
- Could be less reliable at temperature extremes

### Recommendation
- **For prototyping:** Use direct 3.3V connection (current setup)
- **For production (200 units):** Consider adding BSS138 level shifters for robustness
- **For custom PCB:** Include level shifter footprint but make it optional (can bridge if not needed)

---

## Tested Configuration

### Hardware Validated
- ✅ MCP4728 detected at I2C address 0x60
- ✅ All 4 DAC channels output 0-5V range
- ✅ Voltage accuracy within ±0.05V of expected
- ✅ Gate output toggles reliably between 0V and 5V
- ✅ No I2C communication errors
- ✅ Stable operation over multiple power cycles

### Voltage Measurements
| DAC Value | Expected | Measured | Channel |
|---|---|---|---|
| 0 | 0.00V | 0.00V | All |
| 1024 | 1.25V | ~1.25V | All |
| 2048 | 2.50V | ~2.50V | All |
| 3072 | 3.75V | ~3.75V | All |
| 4095 | 5.00V | ~5.00V | All |

### Code Configuration
```python
import board
import adafruit_mcp4728

i2c = board.I2C()  # Shared I2C bus
dac = adafruit_mcp4728.MCP4728(i2c, address=0x60)

# Configure for 5V external reference (VDD)
for channel in [dac.channel_a, dac.channel_b, dac.channel_c, dac.channel_d]:
    channel.vref = adafruit_mcp4728.Vref.VDD  # Use VDD as reference
    channel.gain = 1  # 1x gain

# Set output voltage
# value = (desired_voltage / 5.0) * 4095
dac.channel_a.value = 2048  # 2.5V output
```

---

## Wiring Details

### Full Wiring Diagram
```
┌─────────────────────────────────┐
│  Feather M4 CAN Express         │
│                                 │
│  ┌─────────────────────────┐   │
│  │  OLED FeatherWing       │   │ (stacked)
│  │  128x64 (0x3C)          │   │
│  └─────────────────────────┘   │
│                                 │
│  Stacking Headers:              │
│    D21 (SDA) ───────────────────┼─┐
│    D22 (SCL) ───────────────────┼─┤
│    GND ─────────────────────────┼─┤
│    BAT ─────────┐               │ │
└─────────────────┼───────────────┘ │
                  │                 │
        ┌─────────┴─────────┐       │
        │  Powerboost 5V    │       │
        │  VIN: 3.7-4.2V    │       │
        │  VOUT: 5.18V      │       │
        │  GND ─────────────┼───┐   │
        │  VOUT ────────────┼─┐ │   │
        └───────────────────┘ │ │   │
                              │ │   │
            ┌─────────────────┼─┼───┘
            │                 │ │
    ┌───────┴───────────┐     │ │
    │  MCP4728 DAC      │     │ │
    │  I2C: 0x60        │     │ │
    │                   │     │ │
    │  VDD ←────────────┼─────┘ │
    │  GND ←────────────┼───────┘
    │  SDA ←────────────┤ (from M4 D21)
    │  SCL ←────────────┤ (from M4 D22)
    │                   │
    │  VA  → CV Pitch   │
    │  VB  → Gate/Trig  │
    │  VC  → Velocity   │
    │  VD  → Mod        │
    └───────────────────┘
```

### Connection Checklist
- [ ] Powerboost VIN connected to M4 BAT pin
- [ ] Powerboost GND connected to M4 GND
- [ ] Powerboost configured for 5V output (pads A=0, B=0)
- [ ] Powerboost VOUT connected to MCP4728 VDD
- [ ] Powerboost GND connected to MCP4728 GND
- [ ] M4 D21 (SDA) jumpered to MCP4728 SDA
- [ ] M4 D22 (SCL) jumpered to MCP4728 SCL
- [ ] M4 GND connected to MCP4728 GND (common ground)
- [ ] STEMMA QT cable NOT connected (voltage conflict!)

---

## Test Results

### Test Script
Location: `/tests/mcp4728_with_oled_display.py`

### Test Sequence
1. ✅ I2C bus scan (detects OLED at 0x3C, MCP4728 at 0x60)
2. ✅ MCP4728 initialization
3. ✅ Configuration for VDD reference, 1x gain
4. ✅ Voltage sweep 0V → 5V on Channel A
5. ✅ All 4 channels tested at 2.5V
6. ✅ Gate test on Channel B (0V/5V toggle, 5 cycles)

### Result
**ALL TESTS PASSED** - MCP4728 is ready for CV/Gate integration!

---

## Next Steps

1. ✅ Hardware validated
2. ✅ Test code created
3. 📋 Create CV/Gate driver module for main code
4. 📋 Implement V/Oct scaling for MIDI → CV conversion
5. 📋 Integrate into arpeggiator
6. 📋 Test with actual modular synth

---

## Files Created This Session

- `tests/mcp4728_auto_detect_test.py` - Auto-detects MCP4728 at any address
- `tests/mcp4728_with_oled_display.py` - Full test with OLED feedback
- `tests/i2c_shared_scan.py` - I2C scanner using shared bus
- `docs/hardware/pinouts/PINOUT_REFERENCE.md` - Complete pinout reference
- `docs/hardware/MCP4728_WORKING_SETUP.md` - This document

---

**Document Version:** 1.0
**Last Updated:** 2025-10-24
**Status:** Production-ready setup documented
