keegandewitt/Arp/prisme/drivers/cv_output.py

"""
CV Output Driver for MCP4728 DAC

Generates 1V/octave control voltage for modular synthesizers.
Includes display throttling to prevent I2C bus contention.

Required CircuitPython Libraries:
- adafruit_mcp4728 (install via: circup install adafruit_mcp4728)

Built-in Dependencies:
- board, time, supervisor
"""

import time
import supervisor
import adafruit_mcp4728


class CVOutput:
    """
    1V/octave CV output driver with display throttling

    Features:
    - Pre-calculated MIDI lookup table (zero latency)
    - Direct raw_value control (no bit-shifting)
    - Display update throttling (prevents I2C blocking)
    - Separate channels for CV pitch and Gate output

    Timing Performance:
    - CV update: < 1ms (TIER 1: Real-time critical)
    - Display throttling: 10Hz max (TIER 2: Non-critical)
    """

    # Pre-calculated MIDI note to raw_value lookup (0-127)
    # Formula: raw_value = MIDI_note * 68.27 (for 1V/octave with 5V reference)
    # Clamped to 4095 (12-bit DAC maximum)
    MIDI_TO_CV = [min(int(n * 68.27), 4095) for n in range(128)]

    # Display throttling constants
    DISPLAY_UPDATE_INTERVAL_MS = 100  # 100ms = 10Hz max update rate

    def __init__(self, i2c, display=None, address=0x60, gate_mode='V-TRIG'):
        """
        Initialize MCP4728 for CV output with optional display integration

        Args:
            i2c: Shared I2C bus (from board.I2C())
            display: Optional Display object for throttled updates
            address: MCP4728 I2C address (default 0x60)
            gate_mode: 'V-TRIG' (standard, high=on) or 'S-TRIG' (inverted, low=on)
        """
        self.dac = adafruit_mcp4728.MCP4728(i2c, address=address)
        self.display = display
        self.gate_mode = gate_mode.upper()

        # Wake from power-down mode (critical for new DACs)
        self.dac.wakeup()
        time.sleep(0.1)

        # Configure all channels for 5V operation
        for channel in [self.dac.channel_a, self.dac.channel_b,
                       self.dac.channel_c, self.dac.channel_d]:
            channel.vref = adafruit_mcp4728.Vref.VDD  # Use VDD (5V) reference
            channel.gain = 1  # 1x gain (0-5V output range)
        time.sleep(0.1)

        # Save configuration to EEPROM (survives power cycle)
        self.dac.save_settings()
        time.sleep(0.3)

        # Initialize outputs to safe state
        self.set_cv_a(0)
        self.set_cv_b(0)
        self.set_gate(False)

        # Display throttling state
        self.last_display_update = 0
        self.pending_display_note = None
        self.display_dirty = False

        # Performance tracking (for debugging)
        self.cv_update_count = 0
        self.display_update_count = 0

    def set_cv_a(self, midi_note):
        """
        Set CV output A from MIDI note number (TIER 1: Real-time critical)

        Args:
            midi_note: MIDI note number (0-127)

        Output voltage: (midi_note / 12) volts (1V/octave standard)
        Example: midi_note=60 (C4) → 5.00V

        Timing: < 1ms (measured 0.7ms on Feather M4)
        """
        if 0 <= midi_note <= 127:
            # CRITICAL: Use raw_value for direct 12-bit control
            # Do NOT use .value (16-bit) - causes bit-shifting bug
            self.dac.channel_a.raw_value = self.MIDI_TO_CV[midi_note]
            self.cv_update_count += 1

            # Flag display for later update (non-blocking)
            if self.display is not None:
                self.pending_display_note = midi_note
                self.display_dirty = True

    def set_cv_b(self, midi_note):
        """
        Set CV output B from MIDI note number (TIER 1: Real-time critical)

        Args:
            midi_note: MIDI note number (0-127)
        """
        if 0 <= midi_note <= 127:
            self.dac.channel_b.raw_value = self.MIDI_TO_CV[midi_note]
            self.cv_update_count += 1

    def set_gate(self, state):
        """
        Set gate output (TIER 1: Real-time critical)

        Args:
            state: True = gate on, False = gate off

        Gate modes:
            V-TRIG (standard): True = 5V, False = 0V
            S-TRIG (inverted): True = 0V, False = 5V (for ARP 2600, Korg MS-20)

        Timing: < 1ms
        """
        if self.gate_mode == 'S-TRIG':
            # Inverted gate: 0V = on, 5V = off
            self.dac.channel_c.raw_value = 0 if state else 4095
        else:
            # Standard gate: 5V = on, 0V = off
            self.dac.channel_c.raw_value = 4095 if state else 0

    def set_trigger(self, state):
        """
        Set trigger output on channel D (TIER 1: Real-time critical)

        Args:
            state: True = 5V (trigger high), False = 0V (trigger low)
        """
        self.dac.channel_d.raw_value = 4095 if state else 0

    def set_raw_voltage(self, channel, voltage):
        """
        Set exact voltage on channel (for testing/calibration)

        Args:
            channel: 'a', 'b', 'c', or 'd'
            voltage: Voltage in volts (0.0 to 5.0)
        """
        raw_value = int((voltage / 5.0) * 4095)
        raw_value = max(0, min(4095, raw_value))  # Clamp to valid range

        if channel == 'a':
            self.dac.channel_a.raw_value = raw_value
        elif channel == 'b':
            self.dac.channel_b.raw_value = raw_value
        elif channel == 'c':
            self.dac.channel_c.raw_value = raw_value
        elif channel == 'd':
            self.dac.channel_d.raw_value = raw_value

    def update_display_throttled(self):
        """
        Update display with throttling (TIER 2: Non-critical)

        Call this in main loop. Updates display max 10Hz to prevent
        I2C blocking of CV output.

        Timing: 86.6ms blocking, but only 10% of time
        """
        if not self.display or not self.display_dirty:
            return

        now = supervisor.ticks_ms()
        elapsed = now - self.last_display_update

        if elapsed >= self.DISPLAY_UPDATE_INTERVAL_MS:
            # Update display with pending note
            # This blocks for ~86ms but only happens every 100ms
            if self.pending_display_note is not None:
                self.display.update_pattern(f"Note: {self.pending_display_note}")

            self.last_display_update = now
            self.display_dirty = False
            self.display_update_count += 1

    def get_stats(self):
        """
        Get performance statistics (for debugging)

        Returns:
            dict: CV updates, display updates, update ratio
        """
        if self.display_update_count > 0:
            ratio = self.cv_update_count / self.display_update_count
        else:
            ratio = float('inf')

        return {
            'cv_updates': self.cv_update_count,
            'display_updates': self.display_update_count,
            'cv_to_display_ratio': ratio
        }


# Usage Example
if __name__ == "__main__":
    import board

    print("CV Output Driver - Test Mode")
    print("=" * 60)

    # Initialize I2C bus
    i2c = board.I2C()

    # Create CV output driver (no display for testing)
    cv = CVOutput(i2c, display=None)

    print("Testing CV output with chromatic scale...")
    print("Notes: C2 (36) → C5 (72)")
    print()

    # Play chromatic scale from C2 to C5
    for midi_note in range(36, 73):  # C2 to C5
        note_name = ["C", "C#", "D", "D#", "E", "F", "F#", "G", "G#", "A", "A#", "B"][midi_note % 12]
        octave = (midi_note // 12) - 1
        voltage = midi_note / 12.0

        print(f"Note {midi_note:3d} ({note_name}{octave}) → {voltage:.2f}V")

        # Set CV and gate
        cv.set_cv_a(midi_note)
        cv.set_gate(True)
        time.sleep(0.2)

        cv.set_gate(False)
        time.sleep(0.05)

    # Reset to silence
    cv.set_cv_a(0)
    cv.set_gate(False)

    print("\n" + "=" * 60)
    print("Test complete!")
    print("\nPerformance stats:")
    stats = cv.get_stats()
    print(f"  CV updates: {stats['cv_updates']}")
    print(f"  Display updates: {stats['display_updates']}")
