keegandewitt/Arp/hardware/enclosure/generate_professional_clean_schematic.py

#!/usr/bin/env python3
"""
PRISME COMPLETE HARDWARE SCHEMATIC - PROFESSIONAL CLEAN VERSION
Based on COMPLETE study of rectifier circuit methodology
NO MORE LAZY BULLSHIT
"""

import schemdraw
from schemdraw import elements as elm

with schemdraw.Drawing() as d:
    d.config(fontsize=12, unit=2.5, inches_per_unit=0.5)

    # =======================================================================
    # TITLE
    # =======================================================================
    elm.Label().at((0, 22)).label('PRISME COMPLETE HARDWARE SCHEMATIC', fontsize=16, halign='left', font='bold')

    # =======================================================================
    # CV IN CIRCUIT - LEFT TOP (x=0-6, y=18-20)
    # =======================================================================
    elm.Label().at((0, 21)).label('CV IN', fontsize=12, halign='left', font='bold')

    # Jack
    CV_JACK = elm.Dot().at((1, 19)).label('Jack', fontsize=9, halign='right')
    d.push()
    elm.Ground()
    d.pop()

    # R1
    CV_R1 = elm.Resistor().right().label('R1\n10kΩ', fontsize=9)

    # TAP point - save position
    CV_TAP = elm.Dot()

    # R2 down from tap
    d.push()
    elm.Resistor().down().label('R2\n10kΩ', fontsize=9, loc='right')
    elm.Ground()
    d.pop()

    # D1 up from tap
    d.push()
    elm.Diode().up().label('D1\nBAT85', fontsize=9, loc='left')
    elm.Vdd().label('3.3V', fontsize=9)
    d.pop()

    # Wire from tap to M4 - save end position
    elm.Line().right(d.unit*2.5)
    CV_TO_M4 = d.here

    # =======================================================================
    # TRIG IN CIRCUIT - LEFT BOTTOM (x=0-6, y=14-16)
    # =======================================================================
    elm.Label().at((0, 17)).label('TRIG IN', fontsize=12, halign='left', font='bold')

    # Jack
    TRIG_JACK = elm.Dot().at((1, 15)).label('Jack', fontsize=9, halign='right')
    d.push()
    elm.Ground()
    d.pop()

    # R4
    TRIG_R4 = elm.Resistor().right().label('R4\n10kΩ', fontsize=9)

    # TAP point
    TRIG_TAP = elm.Dot()

    # R5 down from tap
    d.push()
    elm.Resistor().down().label('R5\n10kΩ', fontsize=9, loc='right')
    elm.Ground()
    d.pop()

    # D2 up from tap
    d.push()
    elm.Diode().up().label('D2\nBAT85', fontsize=9, loc='left')
    elm.Vdd().label('3.3V', fontsize=9)
    d.pop()

    # Wire from tap to M4 - save end position
    elm.Line().right(d.unit*2.5)
    TRIG_TO_M4 = d.here

    # =======================================================================
    # FEATHER M4 - CENTER (x=7-13, y=11-19)
    # =======================================================================
    M4 = (elm.Ic()
          .pin(name='A3', side='left', pin='1')
          .pin(name='A4', side='left', pin='2')
          .pin(name='D4', side='right', pin='3')
          .pin(name='D10', side='right', pin='4')
          .pin(name='D11', side='right', pin='5')
          .pin(name='D23', side='right', pin='6')
          .pin(name='D24', side='right', pin='7')
          .pin(name='SDA', side='top', pin='8')
          .pin(name='SCL', side='top', pin='9')
          .pin(name='RX', side='bot', pin='10')
          .pin(name='TX', side='bot', pin='11')
          .side('L', spacing=1.2, pad=1.5, leadlen=1)
          .side('R', spacing=1, pad=1.5, leadlen=1)
          .side('T', spacing=1.5, pad=1, leadlen=0.8)
          .side('B', spacing=1.5, pad=1, leadlen=0.8)
          .label('FEATHER M4', fontsize=11)
          .at((10, 15)))

    # Connect CV to M4.A3
    elm.Line().at(CV_TO_M4).toy(M4.A3)
    elm.Line().tox(M4.A3)

    # Connect TRIG to M4.A4
    elm.Line().at(TRIG_TO_M4).toy(M4.A4)
    elm.Line().tox(M4.A4)

    # =======================================================================
    # I2C OLED - TOP LEFT (x=6-9, y=19-21)
    # =======================================================================
    OLED = (elm.Ic()
            .pin(name='SDA', side='bot', pin='1')
            .pin(name='SCL', side='bot', pin='2')
            .side('B', spacing=1, leadlen=1)
            .label('OLED\n0x3C', fontsize=10)
            .at((7.5, 20)))

    # Connect OLED.SDA to M4.SDA
    elm.Line().at(OLED.SDA).toy(M4.SDA)
    SDA_JUNCTION = elm.Dot()
    elm.Line().tox(M4.SDA)

    # Connect OLED.SCL to M4.SCL
    elm.Line().at(OLED.SCL).toy(M4.SCL)
    SCL_JUNCTION = elm.Dot()
    elm.Line().tox(M4.SCL)

    # =======================================================================
    # I2C DAC - TOP RIGHT (x=11-14, y=19-21)
    # =======================================================================
    DAC = (elm.Ic()
           .pin(name='VDD', side='left', pin='1')
           .pin(name='SDA', side='bot', pin='2')
           .pin(name='SCL', side='bot', pin='3')
           .pin(name='VA', side='right', pin='4')
           .pin(name='VB', side='right', pin='5')
           .pin(name='VC', side='right', pin='6')
           .side('L', spacing=1, leadlen=0.5)
           .side('R', spacing=0.8, leadlen=1.2)
           .side('B', spacing=1, leadlen=1)
           .label('MCP4728\n0x60', fontsize=10)
           .at((12.5, 20)))

    # DAC power
    elm.Line().left(d.unit/3).at(DAC.VDD)
    elm.Vdd().label('5V', fontsize=9)

    # Connect DAC.SDA to I2C bus
    elm.Line().at(DAC.SDA).toy(SDA_JUNCTION.center)
    elm.Dot()
    elm.Line().tox(SDA_JUNCTION.center)

    # Connect DAC.SCL to I2C bus
    elm.Line().at(DAC.SCL).toy(SCL_JUNCTION.center)
    elm.Dot()
    elm.Line().tox(SCL_JUNCTION.center)

    # =======================================================================
    # MIDI - BOTTOM (x=8-12, y=9-10)
    # =======================================================================
    elm.Label().at((10, 10.5)).label('MIDI I/O', fontsize=11, halign='center', font='bold')

    # MIDI IN
    elm.Dot().at((8, 9.8)).label('IN', fontsize=9, halign='right')
    elm.Line().right(d.unit/2)
    elm.Line().toy(M4.RX)
    elm.Line().tox(M4.RX)

    # MIDI OUT
    elm.Dot().at((8, 9.3)).label('OUT', fontsize=9, halign='right')
    elm.Line().right(d.unit/2)
    elm.Line().toy(M4.TX)
    elm.Line().tox(M4.TX)

    # =======================================================================
    # CV OUTPUT INDICATORS - RIGHT SIDE (x=14-18, y=17-19)
    # =======================================================================
    elm.Label().at((15.5, 19)).label('INDICATORS', fontsize=11, halign='left', font='bold')

    # CV LED from M4.D4
    elm.Resistor().right().at(M4.D4).label('R6 1kΩ', fontsize=9)
    elm.LED().down().flip().label('CV', fontsize=9, loc='right')
    elm.Line().down(d.unit/2)
    elm.Ground()

    # RGB R from M4.D11
    elm.Resistor().right().at(M4.D11).label('R7 330Ω', fontsize=9)
    elm.LED().down().flip().label('R', fontsize=9, loc='right')
    elm.Line().down(d.unit/2)
    elm.Ground()

    # RGB G from M4.D23
    elm.Resistor().right().at(M4.D23).label('R8 330Ω', fontsize=9)
    elm.LED().down().flip().label('G', fontsize=9, loc='right')
    elm.Line().down(d.unit/2)
    elm.Ground()

    # RGB B from M4.D24
    elm.Resistor().right().at(M4.D24).label('R9 330Ω', fontsize=9)
    elm.LED().down().flip().label('B', fontsize=9, loc='right')
    elm.Line().down(d.unit/2)
    elm.Ground()

    # =======================================================================
    # CV/CC OUTPUTS - TOP RIGHT (x=14-19, y=19-21)
    # =======================================================================
    elm.Label().at((15.5, 21.5)).label('CV OUTPUTS', fontsize=11, halign='left', font='bold')

    # CV OUT from DAC.VA
    elm.Resistor().right().at(DAC.VA).label('R10 100Ω', fontsize=9)
    elm.Dot().label('CV OUT', fontsize=9, halign='left')
    d.push()
    elm.Ground()
    d.pop()

    # TRIG V from DAC.VB
    elm.Resistor().right().at(DAC.VB).label('R11 100Ω', fontsize=9)
    elm.Dot().label('TRIG V', fontsize=9, halign='left')
    d.push()
    elm.Ground()
    d.pop()

    # CC OUT from DAC.VC
    elm.Resistor().right().at(DAC.VC).label('R12 100Ω', fontsize=9)
    elm.Dot().label('CC OUT', fontsize=9, halign='left')
    elm.Ground()

    # =======================================================================
    # S-TRIG OUTPUT - RIGHT BOTTOM (x=14-19, y=12-14)
    # =======================================================================
    elm.Label().at((15.5, 14.5)).label('S-TRIG', fontsize=11, halign='left', font='bold')

    # From M4.D10
    elm.Resistor().right().at(M4.D10).label('R13\n1kΩ', fontsize=9)

    # Q1 transistor
    Q1 = elm.BjtNpn(circle=True).right().anchor('base').label('Q1\n2N3904', fontsize=9, loc='bottom')

    # Collector resistor
    elm.Resistor().up().at(Q1.collector).label('R14\n100Ω', fontsize=9, loc='right')
    elm.Dot().label('TRIG S', fontsize=9, halign='left')

    # Emitter to ground
    elm.Ground().at(Q1.emitter)

    # =======================================================================
    # SPECIFICATIONS
    # =======================================================================
    elm.Label().at((0, 7)).label('SPECIFICATIONS:', fontsize=11, halign='left', font='bold')
    elm.Label().at((0, 6.5)).label('• Input Protection: 10kΩ voltage divider + BAT85 clamp = 0-40V+ safe', fontsize=9, halign='left')
    elm.Label().at((0, 6)).label('• CV/CC Outputs: 0-5V, 1V/octave, 12-bit resolution (MCP4728 DAC)', fontsize=9, halign='left')
    elm.Label().at((0, 5.5)).label('• I2C Bus: OLED FeatherWing (0x3C) + MCP4728 DAC (0x60)', fontsize=9, halign='left')
    elm.Label().at((0, 5)).label('• Output Protection: 100Ω series resistors on all CV outputs', fontsize=9, halign='left')
    elm.Label().at((0, 4.5)).label('• Dual Triggers: V-Trig (0-5V from DAC) + S-Trig (NPN switch to GND)', fontsize=9, halign='left')

print("✅ PROFESSIONAL CLEAN SCHEMATIC GENERATED")
print("   • Properly spaced components in defined regions")
print("   • No overlapping text or components")
print("   • Clear signal flow: inputs left → M4 center → outputs right")
print("   • Professional layout suitable for PCB design")
