keegandewitt/Arp/scripts/install_libs.py

#!/usr/bin/env python3
"""
CircuitPython Library Installation Helper
Automatically downloads and installs required libraries for the MIDI Arpeggiator

Usage:
    python3 install_libs.py [OPTIONS]

Options:
    --bundle-path PATH    Path to downloaded CircuitPython bundle (if already downloaded)
    --circuitpy-path PATH Path to CIRCUITPY drive (auto-detected if not specified)
    --download            Download the latest bundle automatically
    --help                Show this help message
"""

import os
import sys
import argparse
import shutil
import zipfile
import urllib.request
from pathlib import Path

# Required libraries for this project
REQUIRED_LIBS = [
    {"type": "folder", "name": "adafruit_midi"},
    {"type": "file", "name": "adafruit_displayio_ssd1306.mpy"},
    {"type": "folder", "name": "adafruit_display_text"},
]

# CircuitPython bundle URL (version 10.x)
BUNDLE_URL = "https://github.com/adafruit/Adafruit_CircuitPython_Bundle/releases/latest/download/adafruit-circuitpython-bundle-10.x-mpy-latest.zip"


def find_circuitpy_drive():
    """Auto-detect CIRCUITPY drive on macOS, Linux, or Windows"""
    possible_paths = [
        "/Volumes/CIRCUITPY",  # macOS
        "/media/*/CIRCUITPY",  # Linux
        "D:/",  # Windows (common)
        "E:/",  # Windows (common)
        "F:/",  # Windows (common)
    ]
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
